BMarkley/Z680-Standalone-Subwoofer-Breakout-Board/Z680 Subwoofer/Datasheets/FIT0725.jpg

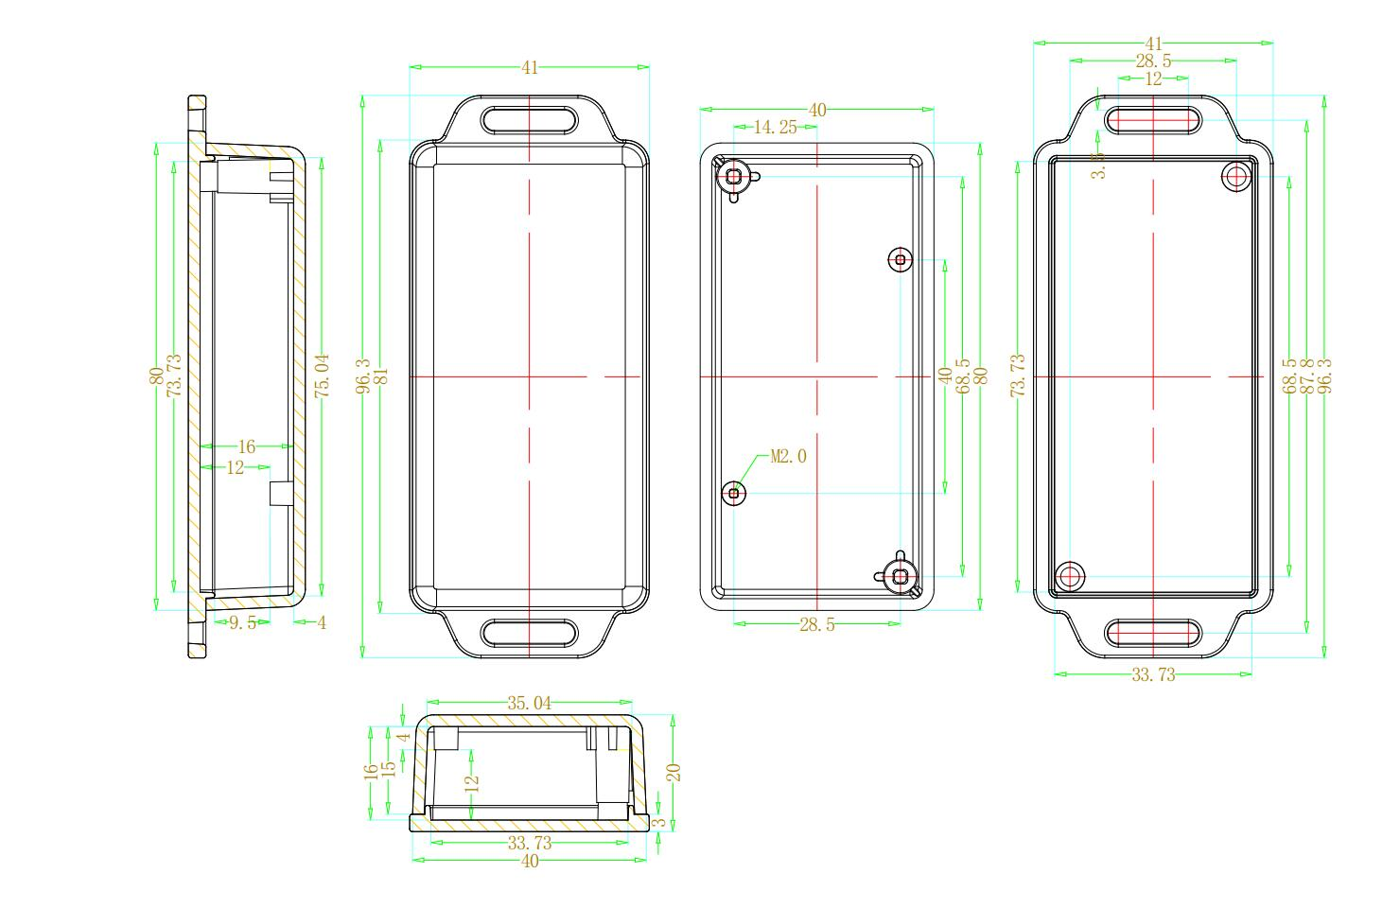
Z680 Subwoofer/Datasheets/FIT0725.jpg
