BMarkley/Z680-Standalone-Subwoofer-Breakout-Board/Z680 Subwoofer/Photos/IMG_20220308_1737323.jpg

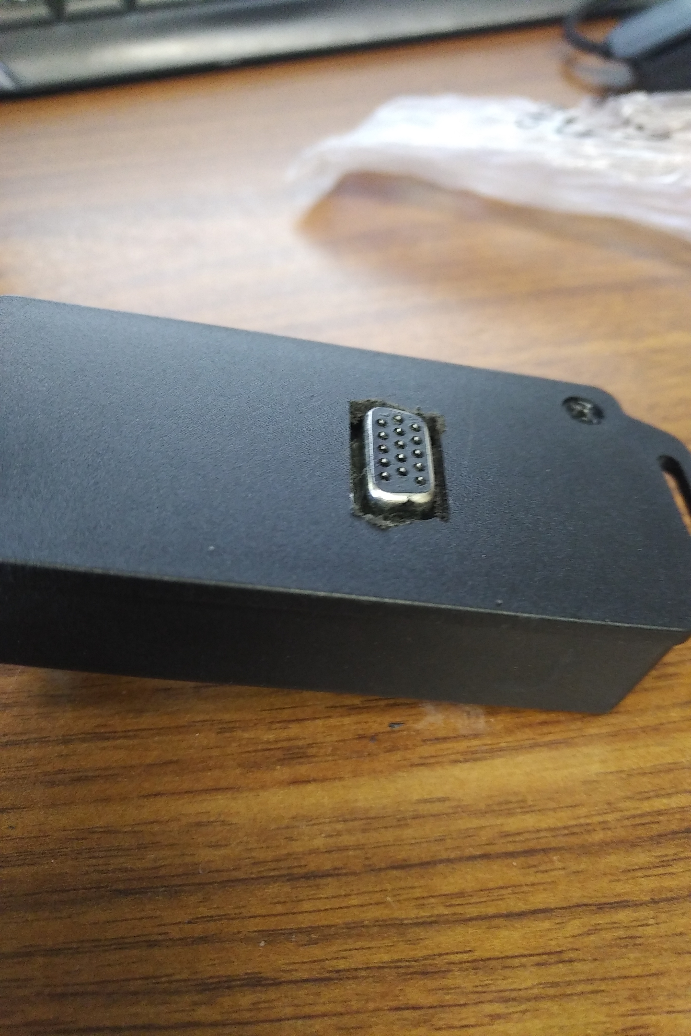
Z680 Subwoofer/Photos/IMG_20220308_1737323.jpg
