BMarkley/Z680-Standalone-Subwoofer-Breakout-Board/Z680 Subwoofer/Photos/IMG_20220308_2135278.jpg

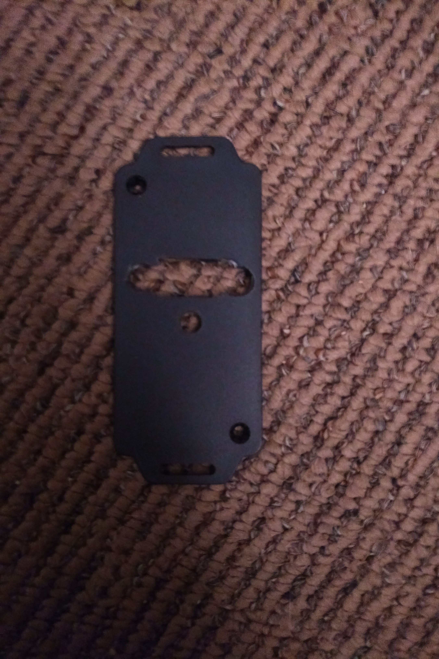
Z680 Subwoofer/Photos/IMG_20220308_2135278.jpg
