BMarkley/Z680-Standalone-Subwoofer-Breakout-Board/Z680 Subwoofer/Photos/IMG_20220308_2136196.jpg

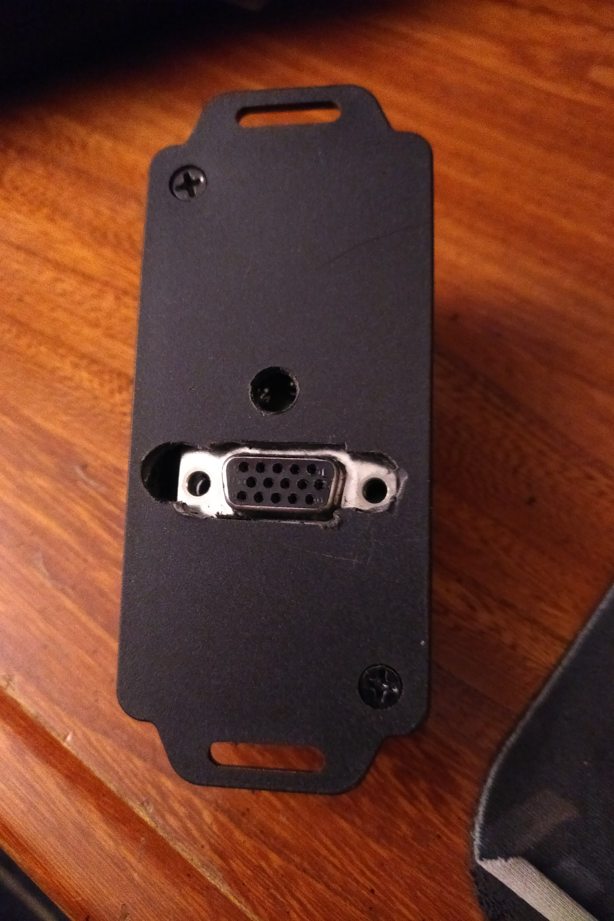
Z680 Subwoofer/Photos/IMG_20220308_2136196.jpg
